CosminCroitoriu/E-Book-Reader/Images/Top View.jpg

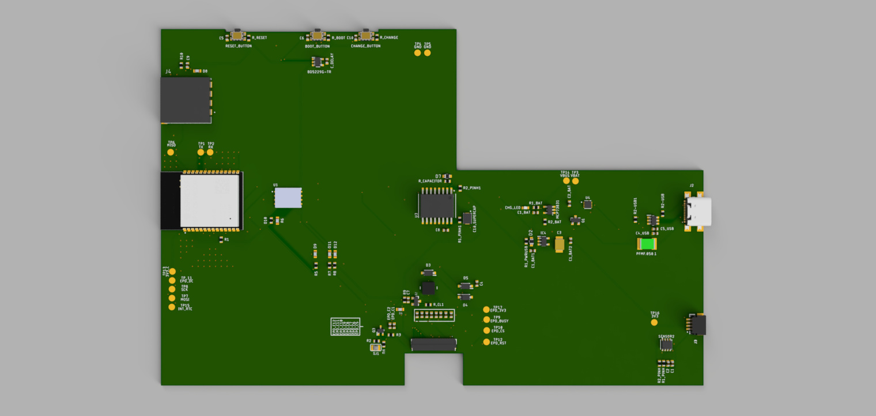
Images/Top View.jpg
